uyupun/open-nose/output/dilator/evolution.png

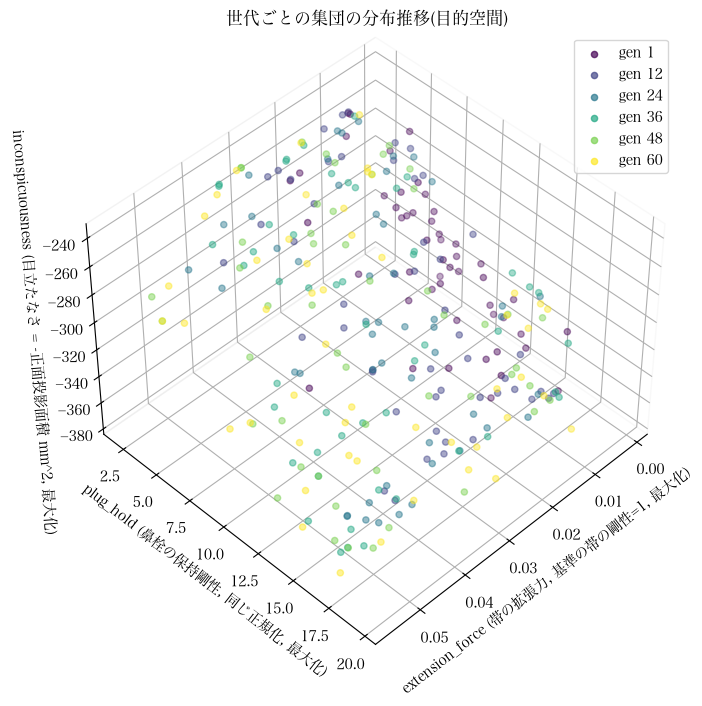
output/dilator/evolution.png
