uyupun/open-nose/output/earrings/evolution.png

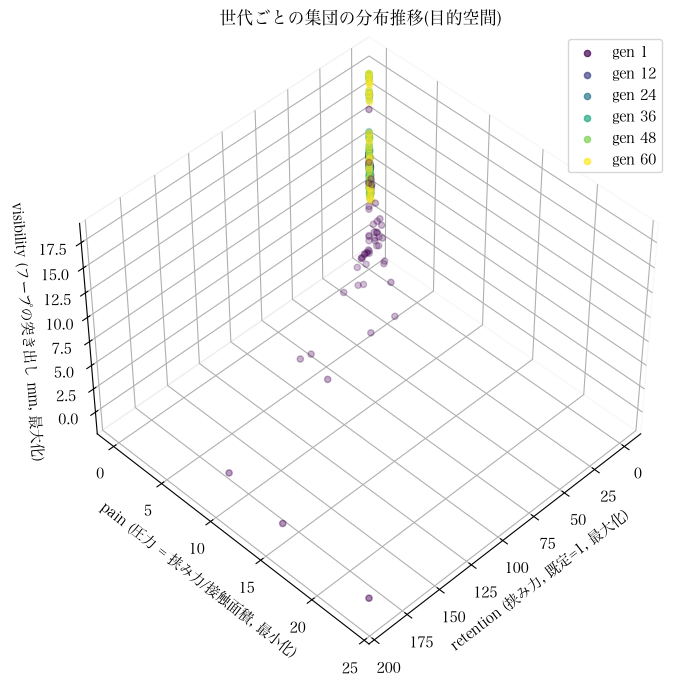
output/earrings/evolution.png
