uyupun/open-nose/output/mizuhiki/evolution.png

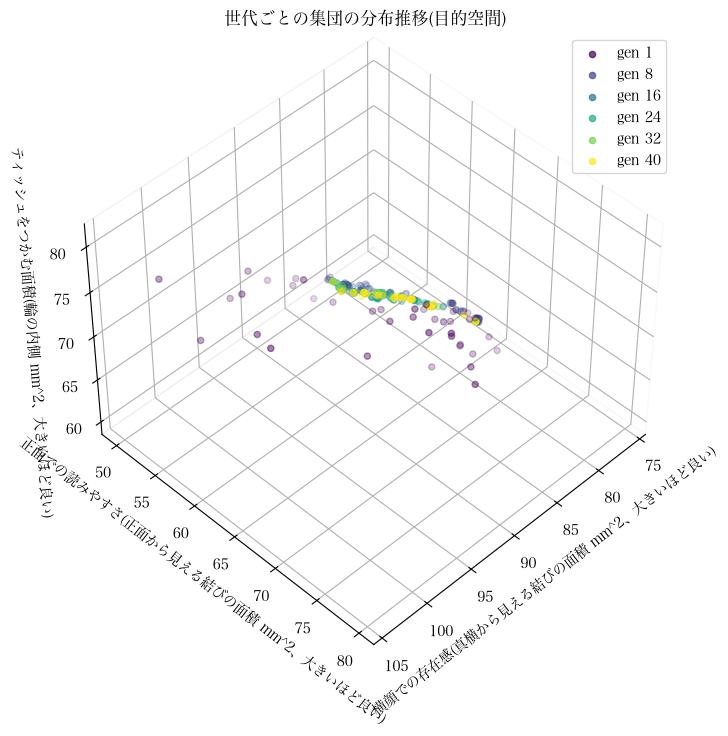
output/mizuhiki/evolution.png
