uyupun/open-nose/output/spiral/evolution.png

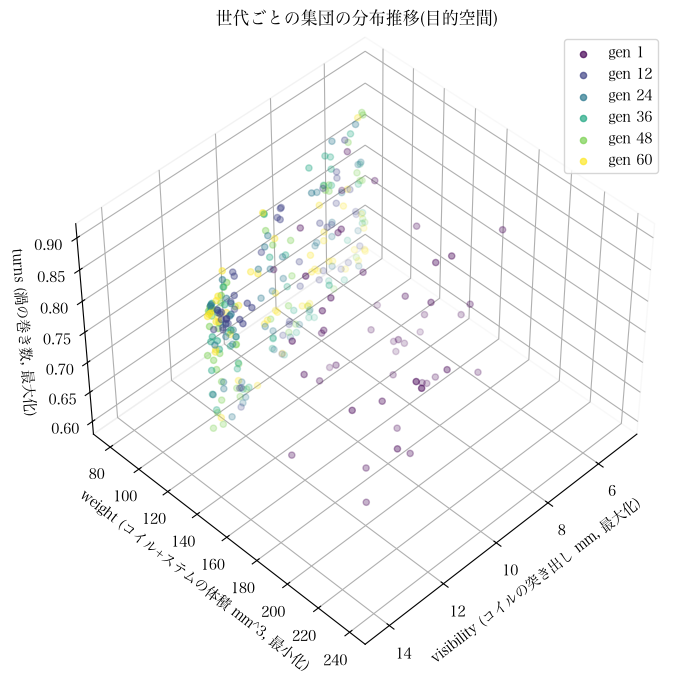
output/spiral/evolution.png
