uyupun/open-nose/output/dilator/candidate_balanced_frame_bridge.stl

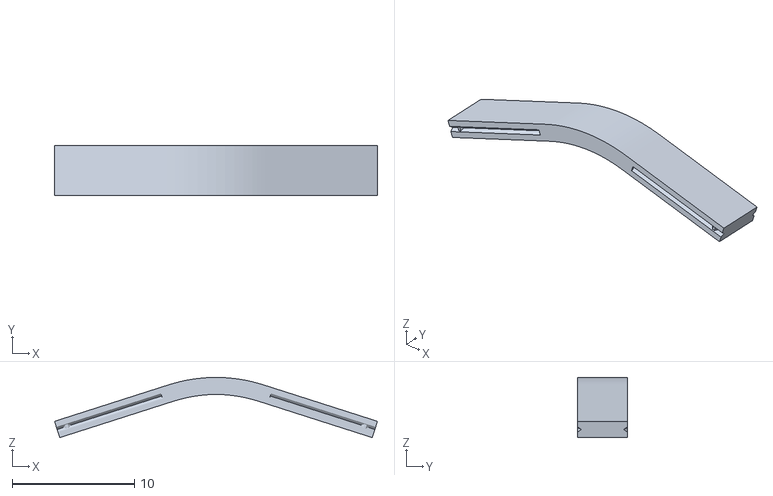
[picture p17: CAD file, 2026-09-27]
output/dilator/candidate_balanced_frame_bridge.stl
26.4 x 4.06 x 4.93
