uyupun/open-nose/output/dilator/connector_cuff_frame_leg_left.stl

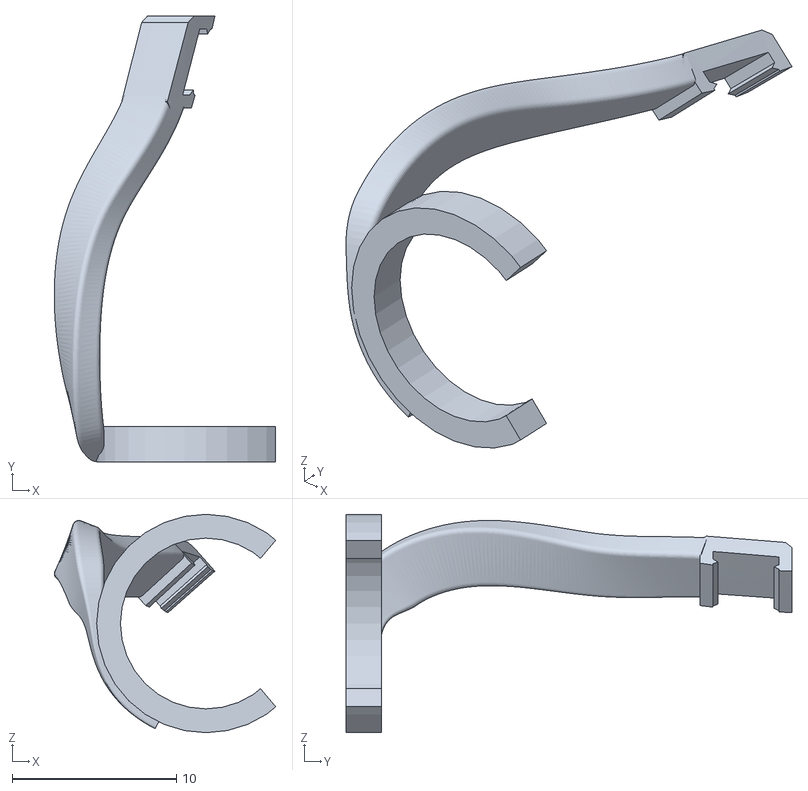
[picture p18: CAD file, 2026-09-27]
output/dilator/connector_cuff_frame_leg_left.stl
13.5 x 27.2 x 13.3
